mdk194/mimi/ergogen/output/images/bottom_plate-bottom.png

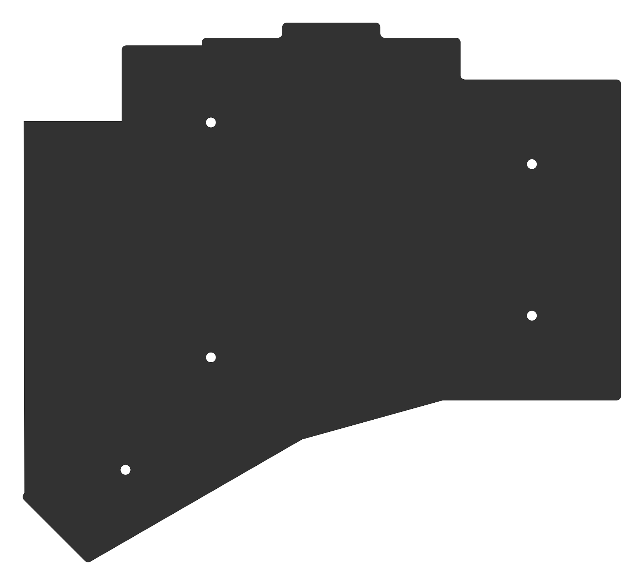
ergogen/output/images/bottom_plate-bottom.png
