mdk194/mimi/ergogen/output/images/bottom_plate-top.png

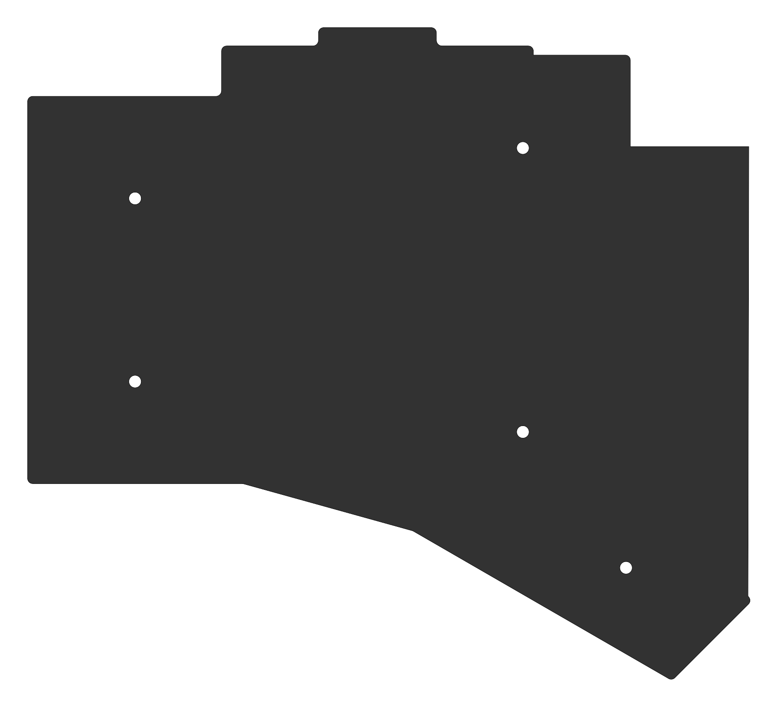
ergogen/output/images/bottom_plate-top.png
