mdk194/mimi/ergogen/output/images/top_plate-bottom.png

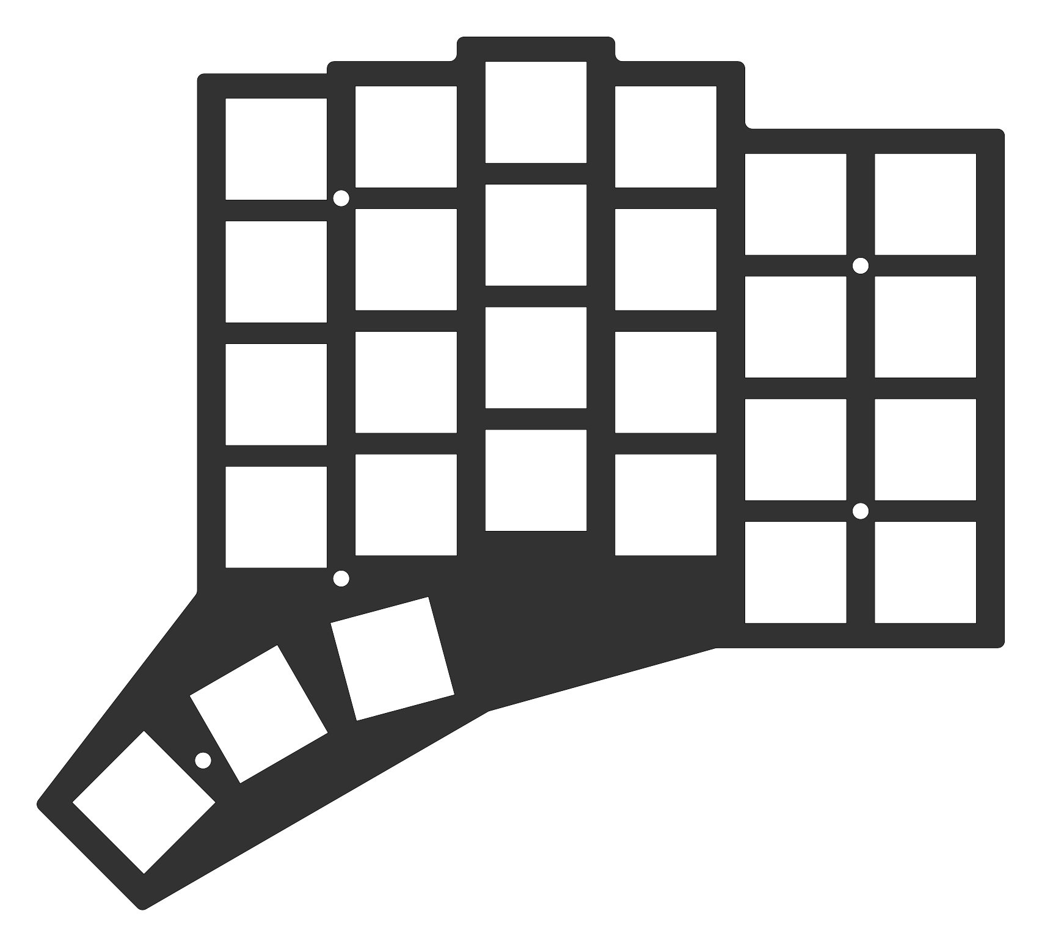
ergogen/output/images/top_plate-bottom.png
