mdk194/mimi/ergogen/output/images/top_plate-top.png

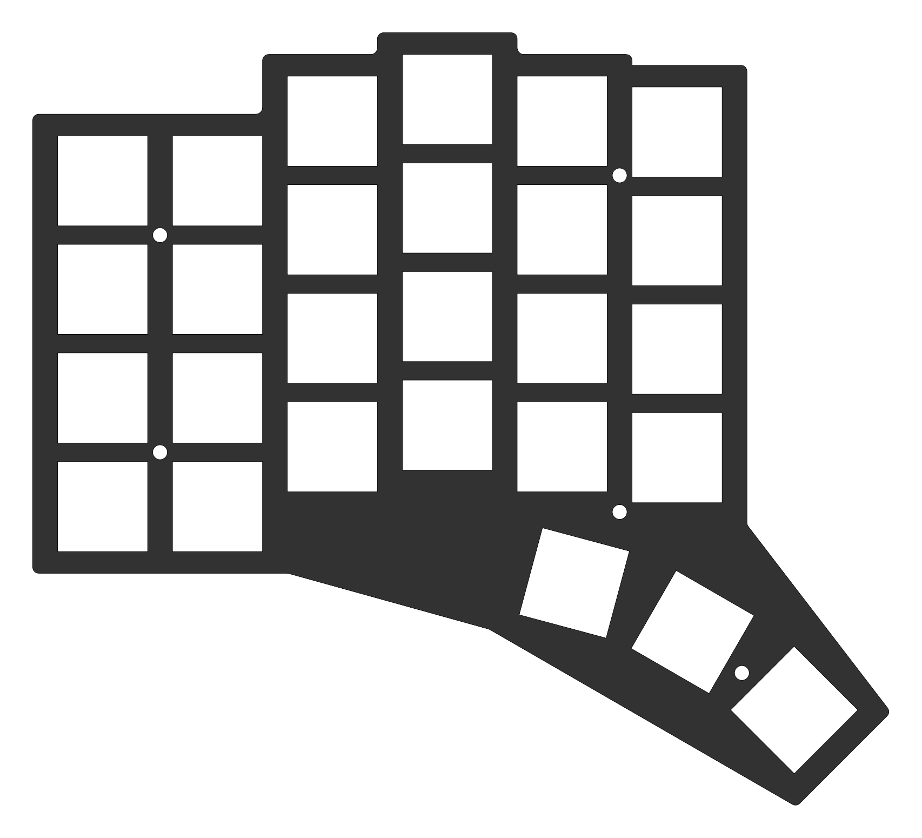
ergogen/output/images/top_plate-top.png
