mdk194/mimi/output/outlines/inner_top_cover_area.dxf

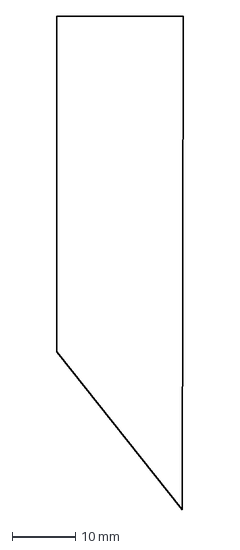
[picture p21: CAD file, 2025-03-17]
output/outlines/inner_top_cover_area.dxf
20.0 x 78.0 mm
