mdk194/mimi/output/outlines/xlbase.dxf

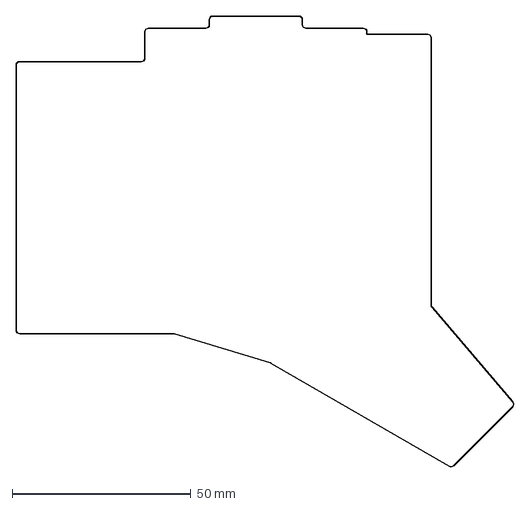
[picture p22: CAD file, 2025-03-17]
output/outlines/xlbase.dxf
139.1 x 126.0 mm
