mdk194/mimi/output/outlines/xlbottom_case.dxf

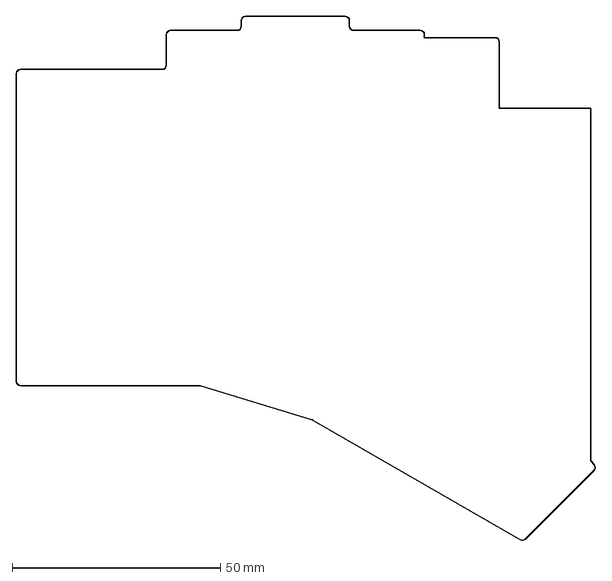
[picture p23: CAD file, 2025-03-17]
output/outlines/xlbottom_case.dxf
139.1 x 126.0 mm
