mdk194/mimi/output/outlines/xlpcb.dxf

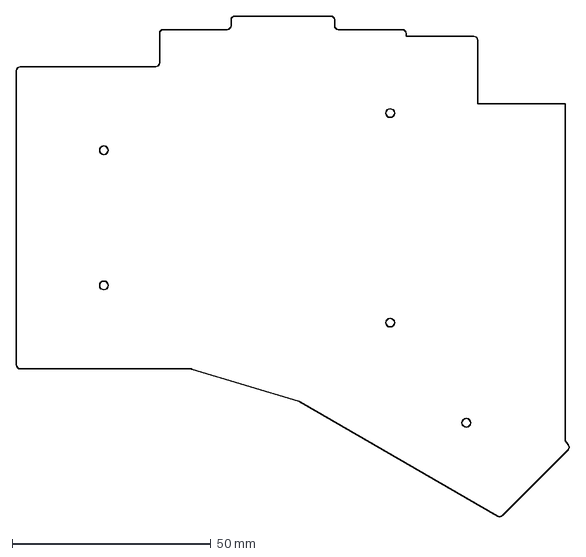
[picture p24: CAD file, 2025-03-17]
output/outlines/xlpcb.dxf
139.1 x 126.0 mm
