mdk194/mimi/output/outlines/switches.dxf

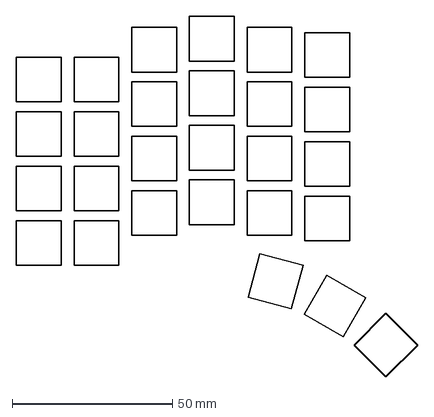
[picture p25: CAD file, 2025-03-17]
output/outlines/switches.dxf
125.2 x 112.5 mm
