mdk194/mimi/output/outlines/xlcontroller_area.dxf

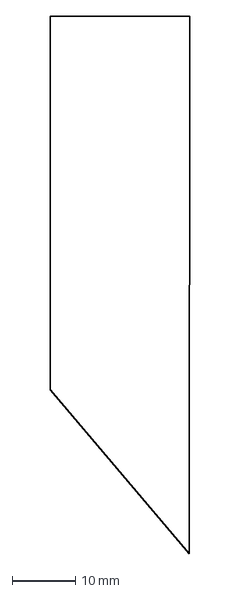
[picture p26: CAD file, 2025-03-17]
output/outlines/xlcontroller_area.dxf
22.0 x 85.0 mm
