mdk194/mimi/output/outlines/top_cover_area.dxf

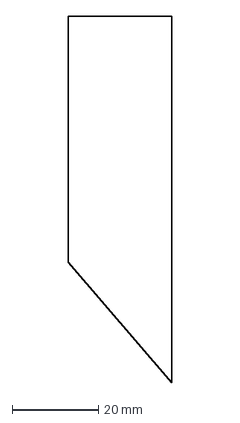
[picture p27: CAD file, 2025-03-17]
output/outlines/top_cover_area.dxf
24.0 x 85.0 mm
