mdk194/mimi/output/outlines/power.dxf

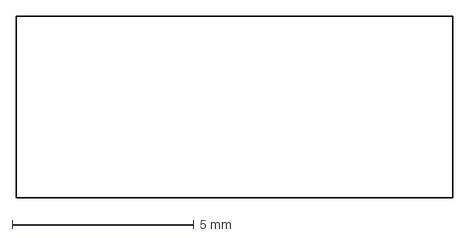
[picture p28: CAD file, 2025-03-17]
output/outlines/power.dxf
12.0 x 5.00 mm
