mdk194/mimi/output/outlines/base.yaml

models:
    export:
        models:
            a:
                models: {}
                origin:
                    - 0
                    - 0
            b:
                paths:
                    p1:
                        type: line
                        origin:
                            - 39
                            - -159.5
                        end:
                            - 39
                            - -89.5
                    p2:
                        type: line
                        origin:
                            - 40
                            - -88.5
                        end:
                            - 74
                            - -88.5
                    p3:
                        type: line
                        origin:
                            - 75
                            - -87.5
                        end:
                            - 75
                            - -80.15
                    p4:
                        type: line
                        origin:
                            - 76
                            - -79.15
                        end:
                            - 92
                            - -79.15
                    p5:
                        type: line
                        origin:
                            - 93
                            - -78.15
                        end:
                            - 93
                            - -76.75
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
                        startAngle: 74.4755783189184
                        endAngle: 90
                        type: arc
                    fillet14:
                        origin:
                            - 40
                            - -159.5
                        radius: 1
                        startAngle: 180
                        endAngle: 270
                        type: arc
                origin:
                    - 0
                    - 0
        origin:
            - 0
            - 0
units: mm
origin:
    - 0
    - 0
