mdk194/mimi/output/outlines/top_case.yaml

models:
    export:
        models:
            a:
                models:
                    a:
                        models:
                            a:
                                models:
                                    a:
                                        models: {}
                                        origin:
                                            - 0
                                            - 0
                                    b:
                                        models:
                                            a:
                                                models: {}
                                                origin:
                                                    - 0
                                                    - 0
                                            b:
                                                paths:
                                                    p1:
                                                        type: line
                                                        origin:
                                                            - 37
                                                            - -161.5
                                                        end:
                                                            - 37
                                                            - -87.5
                                                    p2:
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
                                                                                                                                                                                    - -113.65
                                                                                                                                                                            ShapeLine2:
                                                                                                                                                                                type: line
                                                                                                                                                                                origin:
                                                                                                                                                                                    - 93
                                                                                                                                                                                    - -113.65
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
