mdk194/mimi/output/points/units.yaml

U: 19.05
u: 19
cx: 18
cy: 17
$default_stagger: 0
$default_spread: 19
$default_splay: 0
$default_height: 18
$default_width: 18
$default_padding: 19
$default_autobind: 10
kx: 18
ky: 17
px: 22
py: 21
dpx: 26
dpy: 25
screw_radius: 1.1
screw_diameter: 2.2
screw_head_radius: 2.05
screw_head_diameter: 4.1
spacer_radius: 2.15
spacer_diameter: 4.3
fillet_radius: 0.5
pwr_trace_width: 0.25
gnd_trace_width: 0.25
signal_trace_width: 0.15
